PierceATronics/DIGIMUSER/Hardware/LTSpice/Input_Signal_Conditioner.asc

C1: cap; 1.5n
C2: cap; 680p
C6: cap; 1µ
C7: cap; 180p
CB: cap; 4.7n
CG: cap; 4.7µ
CIN: cap; 22n
PWR: voltage; 3.3
R1: res; 7.68K
R2: res; 14.3K
R4: res; 0
R9: res; 100Meg
R10: res; 100K
R11: res; 10K
RB1: res; 51.1K
RB2: res; 51.1K
RF: res; 11K
RG: res; 1K
RIN: res; 100K
U1: UniversalOpamp2; Avol=316227 GBW=2Meg Slew=1Meg
U3: UniversalOpamp2
V1: voltage; SINE(0 0.050 440); AC 1; Rser=600
V3: voltage; wavefile="Flanger_Demo.wav" chan=0; AC 9.0909
Named nets: 0, VDD, MIC_IN, AMP_OUT, ADC_IN
2nd Order Sallen-Key LPF
Fc=15KHz
DC Bias Mic Signal @ (Vpp/2)
Vpp is the full-scale input to ADC
RC configuration of R4, R9, C6, and C7 are suggested by the design document for the CS5343 ADC.
The ADC will self-bias the voltage of the input signal. The full-scale range is defined as 0.56*VA.
Thus the Vpeak for ADC input is approximate 0.28*VC.
;ac dec 100 1 1Meg
SIMULATE MICROPHONE
.tran 3
